john0312/hitcon-pcb-badge/fw/Core/Hitcon/App/MainMenuApp.h

#ifndef MAIN_MENU_APP_H
#define MAIN_MENU_APP_H

#include <App/BadUsbApp.h>
#include <App/BouncingDVDApp.h>
#include <App/DebugApp.h>
#include <App/DinoApp.h>
#include <App/QrCodeApp.h>
#include <App/ScoreHistApp.h>
#include <App/ShowIdApp.h>
#include <App/ShowNameApp.h>
#include <App/SnakeApp.h>
#include <App/SpaceshipApp.h>
#include <App/TamaApp.h>
#include <App/TetrisApp.h>
#include <Logic/BadgeController.h>

#include "MenuApp.h"

namespace hitcon {

using hitcon::app::bouncing_dvd::bouncing_dvd_app;
using hitcon::app::dino::dino_app;
using hitcon::app::qr::qr_code_app;
using hitcon::app::snake::snake_app;
using hitcon::app::spaceship::spaceship_app;
using hitcon::app::tama::tama_app;
using hitcon::app::tetris::tetris_app;

constexpr menu_entry_t main_menu_entries[] = {
    // TODO : change app
    {"Hacker Pet", &tama_app, &hitcon::app::tama::SetSingleplayer},
    {"Snake", &snake_app, &hitcon::app::snake::SetSingleplayer},
    {"Tetris", &tetris_app, &hitcon::app::tetris::SetSingleplayer},
    {"Spaceship", &spaceship_app, nullptr},
    {"Dino", &dino_app, nullptr},
    {"QR Code", &qr_code_app, nullptr},
    {"Show ID", &show_id_app, nullptr},
    {"Show Scores", &score_hist::g_score_hist, nullptr},
    {"Bouncing DVD", &bouncing_dvd_app, nullptr},
    {"Step Counter", &g_debug_accel_app, nullptr},
    //,{"Debug", &g_debug_app, nullptr}
};

constexpr int main_menu_entries_len =
    sizeof(main_menu_entries) / sizeof(menu_entry_t);

class MainMenuApp : public MenuApp {
 public:
  MainMenuApp()
      : MenuApp(main_menu_entries, main_menu_entries_len), dbg_ctr(0) {}
  void OnButtonMode() override { badge_controller.change_app(&show_name_app); }
  void OnButtonBack() override { badge_controller.change_app(&show_name_app); }
  void OnButtonLongBack() override {
    badge_controller.change_app(&show_name_app);
  }
  void OnButton(button_t button) override;

 private:
  uint8_t dbg_ctr = 0;
};

extern MainMenuApp main_menu;

}  // namespace hitcon
#endif
