john0312/hitcon-pcb-badge/fw/Core/Hitcon/Service/IrService.cc

#include <Logic/RandomPool.h>
#include <Service/IrService.h>
#include <Service/Suspender.h>
#include <main.h>
#include <stm32f1xx_ll_gpio.h>
#include <tim.h>

void HAL_TIM_PWM_PulseFinishedCallback(TIM_HandleTypeDef *htim) {
  if (htim != &htim3) return;
  HAL_TIM_PWM_Stop_DMA(htim, TIM_CHANNEL_3);
}

using namespace hitcon::service::sched;

namespace hitcon {
namespace ir {

IrService irService;

IrService::IrService()
    : dma_tx_populate_task(
          100, (task_callback_t)&IrService::PopulateTxDmaBuffer, this),
      dma_rx_pull_task(150, (task_callback_t)&IrService::PullRxDmaBuffer, this),
      routine_task(600, (callback_t)&IrService::Routine, this, 22),
      on_rx_callback_runner(500, (callback_t)&IrService::OnBufferRecvWrapper,
                            this),
      rx_buffer_base(0), rx_on_buffer_callback_finished(true), rx_quiet_cnt(0),
      rx_required_quiet_period(500), rx_ctr_since_release(100000),
      tx_packet_cnt(0) {}

void ReceiveDmaHalfCplt(DMA_HandleTypeDef *hdma) {
  if (!g_suspender.IsSuspended()) {
    scheduler.Queue(&irService.dma_rx_pull_task, reinterpret_cast<void *>(0));
  }
}

void ReceiveDmaCplt(DMA_HandleTypeDef *hdma) {
  if (!g_suspender.IsSuspended()) {
    scheduler.Queue(&irService.dma_rx_pull_task, reinterpret_cast<void *>(1));
  }
}

void TransmitDmaHalfCplt(DMA_HandleTypeDef *hdma) {
  if (!g_suspender.IsSuspended()) {
    scheduler.Queue(&irService.dma_tx_populate_task,
                    reinterpret_cast<void *>(0));
  }
  //  irService.PopulateTxDmaBuffer(reinterpret_cast<void *>(1));
}

void TransmitDmaCplt(DMA_HandleTypeDef *hdma) {
  if (!g_suspender.IsSuspended()) {
    scheduler.Queue(&irService.dma_tx_populate_task,
                    reinterpret_cast<void *>(1));
  }
  //  irService.PopulateTxDmaBuffer(reinterpret_cast<void *>(1));
}

void IrService::PullRxDmaBuffer(void *ptr_side) {
  int side = reinterpret_cast<intptr_t>(ptr_side);

  size_t k = 0;
  size_t dma_base = (-side) & static_cast<int>(IR_SERVICE_RX_SIZE);
  for (size_t i = 0; i < IR_BYTE_PER_RUN; i++) {
    rx_buffer[rx_buffer_base] = 0;
    for (size_t j = 0; j < 8; j++, k++) {
      bool cbit = !static_cast<bool>(rx_dma_buffer[dma_base + k] & IrRx_Pin);
      rx_buffer[rx_buffer_base] |= (-static_cast<int8_t>(cbit)) & (1 << j);
    }
    if (rx_buffer[rx_buffer_base])
      rx_quiet_cnt = 0;
    else
      rx_quiet_cnt++;

    rx_buffer_base++;
  }
  rx_ctr_since_release++;
  if (rx_ctr_since_release == 1) {
    if ((rx_buffer[38] & 0x0F0) != 0 || (rx_buffer[39] & 0x0F) != 0) {
      // Abort transmission.
      tx_state = 0x02000000;
    }
  }

  rx_buffer_base = rx_buffer_base % (IR_SERVICE_RX_ON_BUFFER_SIZE * 2);
  if (rx_buffer_base % IR_SERVICE_RX_ON_BUFFER_SIZE == 0) {
    my_assert(rx_on_buffer_callback_finished);
    // Trigger the callback.

    // Are we sending the second half to the callback?
    bool is_second = !(rx_buffer_base / IR_SERVICE_RX_ON_BUFFER_SIZE);

    if (!is_second && tx_state >> 24 == 0x01 &&
        rx_quiet_cnt > rx_required_quiet_period) {
      tx_state = 0x03000000;
      rx_ctr_since_release = 0;
    }

    // Compute the buffer.
    uint8_t *buffer_ptr = &rx_buffer[(-static_cast<size_t>(is_second)) &
                                     IR_SERVICE_RX_ON_BUFFER_SIZE];
    rx_on_buffer_callback_finished = false;
    scheduler.Queue(&on_rx_callback_runner, buffer_ptr);
  }
}

void IrService::OnBufferRecvWrapper(void *arg2) {
  if (on_rx_buffer_cb) on_rx_buffer_cb(on_rx_buffer_arg, arg2);
  rx_on_buffer_callback_finished = true;
}

void IrService::Init() {
  hdma_tim2_ch3.XferHalfCpltCallback = &ReceiveDmaHalfCplt;
  hdma_tim2_ch3.XferCpltCallback = &ReceiveDmaCplt;

  hdma_tim3_ch3.XferCpltCallback = &TransmitDmaCplt;
  hdma_tim3_ch3.XferHalfCpltCallback = &TransmitDmaHalfCplt;
  __HAL_TIM_ENABLE_DMA(&htim2, TIM_DMA_CC3);
  HAL_TIM_PWM_Start(&htim2, TIM_CHANNEL_3);
  LL_GPIO_AF_RemapPartial2_TIM2();
  __HAL_TIM_ENABLE_DMA(&htim3, TIM_DMA_CC3);
  HAL_TIM_PWM_Start(&htim3, TIM_CHANNEL_3);
  HAL_DMA_Start_IT(&hdma_tim2_ch3, reinterpret_cast<uint32_t>(&GPIOA->IDR),
                   reinterpret_cast<uint32_t>(rx_dma_buffer),
                   IR_SERVICE_RX_SIZE * 2);
  HAL_DMA_Start_IT(&hdma_tim3_ch3, reinterpret_cast<uint32_t>(tx_dma_buffer),
                   reinterpret_cast<uint32_t>(&(htim3.Instance->CCR3)),
                   IR_SERVICE_TX_SIZE * 2);
  scheduler.Queue(&routine_task, nullptr);
  scheduler.EnablePeriodic(&routine_task);
}

bool IrService::CanSendBufferNow() { return tx_state == 0x00000000; }

bool IrService::SendBuffer(const uint8_t *data, size_t len, bool send_header) {
  if (tx_state != 0x00000000) {
    // Can't send buffer now, we're handling another buffer.
    return false;
  }

  tx_pending_buffer = data;
  tx_pending_buffer_len = len;
  tx_pending_send_header = send_header;

  g_suspender.IncBlocker();
  tx_state = 0x01000000;

  return true;
}

void IrService::SetOnBufferReceived(callback_t callback, void *callback_arg1) {
  on_rx_buffer_cb = callback;
  on_rx_buffer_arg = callback_arg1;
}

void IrService::PopulateTxDmaBuffer(void *ptr_side) {
  int side = reinterpret_cast<intptr_t>(ptr_side);

  uint32_t cstate = tx_state >> 24;
  int dma_base = (-side) & static_cast<int>(IR_SERVICE_TX_SIZE);
  if (cstate <= 2) {
    // Not transmitting.
    for (int i = 0; i < IR_SERVICE_TX_SIZE; i++) {
      tx_dma_buffer[dma_base + i] = 0;
    }
  } else if (cstate == 3) {
    // Send header.
    size_t ctr = tx_state & 0x00FFFFFF;
    size_t base = ctr * IR_PACKET_PER_RUN;
    for (int i = 0; i < IR_SERVICE_TX_SIZE; i++) {
      tx_dma_buffer[dma_base + i] =
          (-static_cast<int16_t>(IR_PACKET_HEADER[base + i / 8])) &
          IR_PWM_TIM_CCR;
    }
    tx_state++;
    if (ctr == IR_PACKET_RUN_COUNT - 1) {
      // Done.
      tx_state = 0x04000000;
    }
  } else if (cstate == 4) {
    // Send body.
    size_t ctr = tx_state & 0x00FFFFFF;
    size_t base_bit = ctr * IR_BITS_PER_TX_RUN;
    int i = 0;
    for (int j = 0; j < IR_BITS_PER_TX_RUN; j++, base_bit++) {
      int cbit = (tx_pending_buffer[base_bit / 8] >> (base_bit % 8)) & 0x01;
      int16_t ccr_val = (-static_cast<int16_t>(cbit)) & IR_PWM_TIM_CCR;
      for (int k = 0; k < PULSE_PER_DATA_BIT; k++, i++) {
        tx_dma_buffer[dma_base + i] = ccr_val;
      }
    }
    tx_state++;
    if (ctr + 1 == (tx_pending_buffer_len * 8 / IR_BITS_PER_TX_RUN)) {
      // Transmission done.
      tx_state = 0x00000000;
      g_suspender.DecBlocker();
      tx_packet_cnt++;
    }
  } else {
    my_assert(false);
  }
}

void IrService::Routine(void *arg1) {
  rx_required_quiet_period = 20 + g_fast_random_pool.GetRandom() % 32;
  if (rx_ctr_since_release >= 100000) rx_ctr_since_release = 100000;

  if (tx_state >> 24 == 0x02) {
    // Collision, let's wait randomly.
    tx_state++;
    int collision_wait = tx_state & 0x00FFFFFF;
    if (collision_wait >= (32 + g_fast_random_pool.GetRandom() % 64)) {
      // Wait's over, retransmit.
      tx_state = 0x01000000;
    }
  }
}

}  // namespace ir
}  // namespace hitcon
