john0312/hitcon-pcb-badge/fw/Core/Hitcon/App/DinoApp.cc

#include "DinoApp.h"

#include <App/MainMenuApp.h>
#include <App/ShowScoreApp.h>
#include <Logic/BadgeController.h>
#include <Logic/Display/display.h>
#include <Logic/GameScore.h>
#include <Logic/RandomPool.h>
#include <Secret/secret.h>
#include <Service/Sched/Scheduler.h>
#include <Util/uint_to_str.h>

#include <cmath>

using namespace hitcon::service::sched;

namespace hitcon {
namespace app {
namespace dino {

int combo_button_ctr = 0;

DinoApp dino_app;

#pragma GCC diagnostic push
#pragma GCC diagnostic ignored "-Wpmf-conversions"
DinoApp::DinoApp()
    : _routine_task(930, (task_callback_t)&DinoApp::Routine, (void*)this,
                    INTERVAL) {}
#pragma GCC diagnostic pop

void DinoApp::Init() { scheduler.Queue(&_routine_task, nullptr); }

void DinoApp::GameEntry() {
  _dino_state = DINO_INIT;
  display_set_mode_scroll_text("Ready...");
}

void DinoApp::AbortGame() { badge_controller.BackToMenu(this); }

void DinoApp::StartGame() {
  memset(_obstacle_frame, 0, OBSTACAL_FRAME_WIDTH * sizeof(uint8_t));
  _curr_dino_frame = &dino_running_bitmap[0];
  _obstacle_interval = 0;
  _generate_obs_rate = 8;
  _game_over = 0;
  _score = 0;
  _dino_state = DINO_RUN;
  _dino_ani_frame = 0;
  _dino_jump_vel = DINO_INITIAL_VEL;
  scheduler.EnablePeriodic(&_routine_task);
}
void DinoApp::GameExit() { scheduler.DisablePeriodic(&_routine_task); }

void DinoApp::OnButton(button_t button) {
  if (_dino_state == DINO_INIT) {
    if ((button & BUTTON_VALUE_MASK) == BUTTON_OK) {
      if (IsMultiplayer()) {
        SendStartGame();
      }
      StartGame();
    }
    return;
  }

  if (button == COMBO_BUTTON_DINO[combo_button_ctr]) {
    combo_button_ctr++;
  } else {
    combo_button_ctr = (button == COMBO_BUTTON_DINO[0]) ? 1 : 0;
  }
  if (combo_button_ctr == COMBO_BUTTON_DINO_LEN) {
    // surprise
    combo_button_ctr = (button == COMBO_BUTTON_DINO[0]) ? 1 : 0;
    _no_big_cactus = true;
  }

  switch (button & BUTTON_VALUE_MASK) {
    case BUTTON_BACK:
    case BUTTON_LONG_BACK:
      if (IsMultiplayer()) {
        SendAbortGame();
      }
      AbortGame();
      break;
    default:
      break;
  }
  return;
}

void DinoApp::OnEdgeButton(button_t button) {
  if (_dino_state == DINO_INIT) return;
  switch (button & BUTTON_VALUE_MASK) {
    case BUTTON_DOWN:
      if (button & BUTTON_KEYDOWN_BIT)
        _dino_state = DINO_CRUNCH;
      else if (button & BUTTON_KEYUP_BIT)
        _dino_state = DINO_RUN;
      break;
    case BUTTON_UP:
      _dino_state = DINO_JUMP;
      break;
  }
}

void DinoApp::Routine(void* unused) {
  if (_game_over) {
    _score_show_time++;
    if (_score_show_time == DINO_SHOW_SCORE_TIME)
      badge_controller.change_app(&dino_app);
    return;
  }
  // Shift frame
  for (uint8_t i = 0; i < OBSTACAL_FRAME_WIDTH - 1; i++) {
    _obstacle_frame[i] = _obstacle_frame[i + 1];
  }
  _obstacle_frame[OBSTACAL_FRAME_WIDTH - 1] = 0;
  _obstacle_interval++;
  // Generate obstacle
  if (_obstacle_interval > DINO_OBS_LEAST_DISTANCE) {
    if ((_obstacle_interval > DISPLAY_WIDTH * 2) ||
        (g_fast_random_pool.GetRandom() % _generate_obs_rate == 0)) {
      switch (g_fast_random_pool.GetRandom() % (_no_big_cactus ? 3 : 4)) {
        case 0:  // bird
          writeObsByte(DISPLAY_WIDTH, bird_bitmap[0]);
          writeObsByte(DISPLAY_WIDTH + 1, bird_bitmap[1]);
          writeObsByte(DISPLAY_WIDTH + 2, bird_bitmap[2]);
          _obstacle_interval = -6;
          break;
        case 1:  // small tall cactus
          writeObsByte(DISPLAY_WIDTH, small_tall_cactus_bitmap[0]);
          _obstacle_interval = -3;
          break;
        case 2:  // small short cactus
          writeObsByte(DISPLAY_WIDTH, small_short_cactus_bitmap[0]);
          _obstacle_interval = -3;
          break;
        case 3:  // big cactus
          writeObsByte(DISPLAY_WIDTH, big_cactus_bitmap[0]);
          writeObsByte(DISPLAY_WIDTH + 1, big_cactus_bitmap[1]);
          writeObsByte(DISPLAY_WIDTH + 2, big_cactus_bitmap[2]);
          _obstacle_interval = -5;
          break;
        default:
          my_assert(false);
      }
    }
  }
  // Determine dinosaur movement
  // Input is only available when dinosaur is on the ground
  if (_dino_jump_vel == DINO_INITIAL_VEL) {
    switch (_dino_state) {
      case DINO_CRUNCH:
        _curr_dino_frame = &dino_crunching_bitmap[_dino_ani_frame];
        break;
      case DINO_JUMP:
        _dino_jump_vel = DINO_HEIGHT - 1;
        _curr_dino_frame = &dino_jumping_bitmap[abs(_dino_jump_vel)];
        break;
      default:
        my_assert(_dino_state == DINO_RUN);
        _curr_dino_frame = &dino_running_bitmap[_dino_ani_frame];
        break;
    }
  } else {
    _dino_jump_vel--;
    if (_dino_jump_vel == DINO_INITIAL_VEL) {
      _curr_dino_frame = &dino_running_bitmap[_dino_ani_frame];
      _dino_state = DINO_RUN;
    } else {
      _curr_dino_frame = &dino_jumping_bitmap[abs(_dino_jump_vel)];
    }
  }

  if (dinoDied()) {
    if (IsMultiplayer()) {
      SendGameOver();
    }
    GameOver();
    return;
  }
  printFrame();
  _dino_ani_frame ^= 1;
  if (_score < 9999) _score++;
}

inline void DinoApp::writeObsByte(uint8_t pos, display_buf_t line) {
  _obstacle_frame[pos] = line;
}

inline void DinoApp::printFrame() {
  display_buf_t frame[DISPLAY_WIDTH] = {0};
  memcpy(frame, _obstacle_frame, sizeof(frame));
  for (uint8_t i = 0; i < DINO_WIDTH; i++) {
    frame[i] |= (*_curr_dino_frame)[i];
  }
  display_set_mode_fixed_packed(frame);
}

bool DinoApp::dinoDied() {
  for (uint8_t i = 0; i < DINO_WIDTH; i++) {
    if (_obstacle_frame[i] & (*_curr_dino_frame)[i]) {
      return true;
    }
  }
  return false;
}

inline void DinoApp::GameOver() {
  _game_over = true;
  _score_show_time = 0;
  show_score_app.SetScore(_score);
  g_game_score.MarkScore(GameScoreType::GAME_DINO, _score);
  badge_controller.change_app(&show_score_app);
}

}  // namespace dino
}  // namespace app
}  // namespace hitcon
